bazystef08/Infoeducatie-2026-BazyQ-Automated-Irrigation-System/PPT/2.png

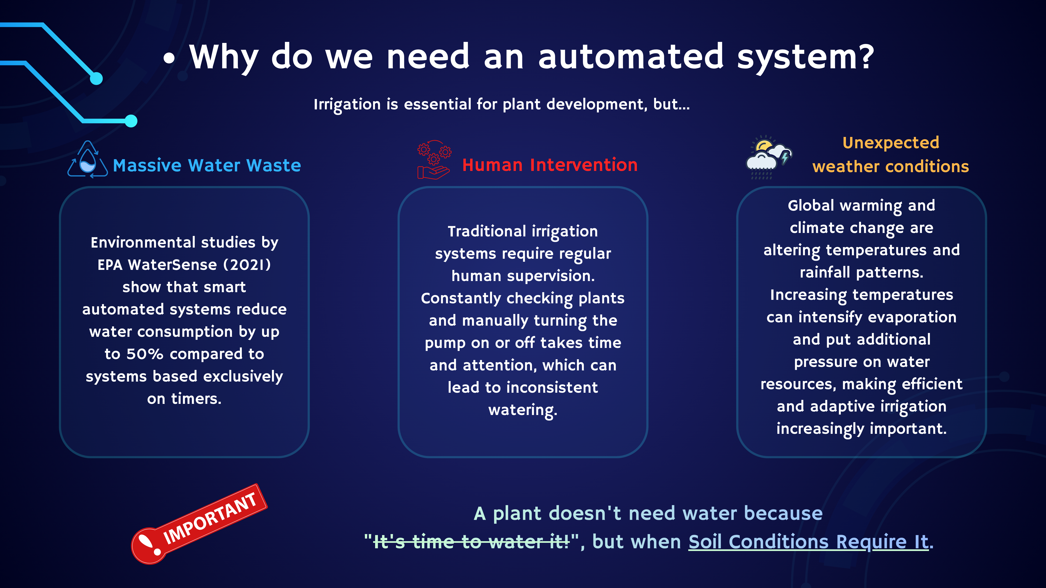
PPT/2.png
