bazystef08/Infoeducatie-2026-BazyQ-Automated-Irrigation-System/PPT/3.png

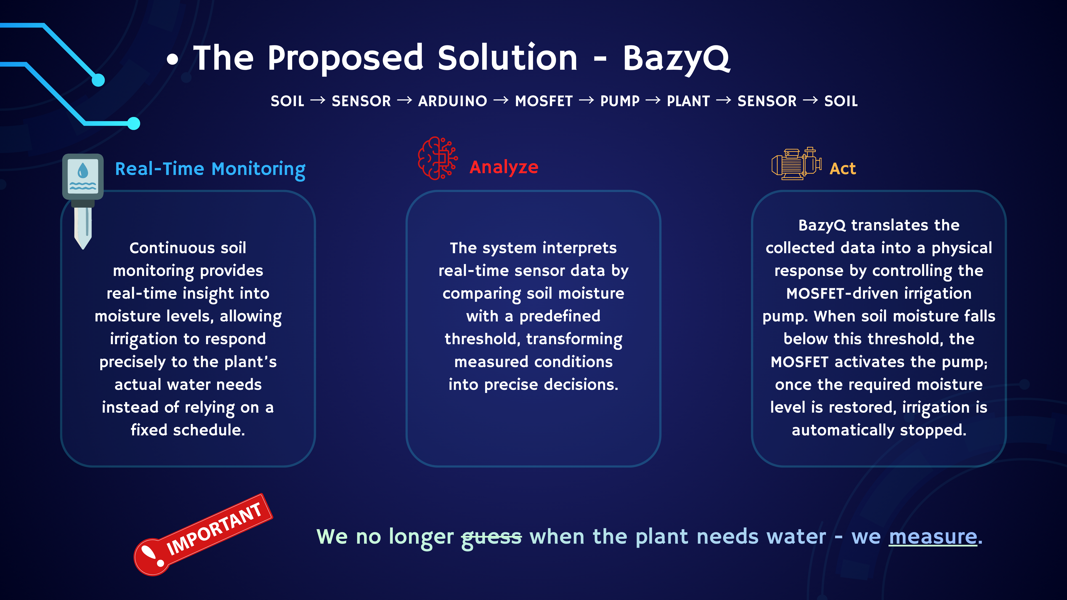
PPT/3.png
