bazystef08/Infoeducatie-2026-BazyQ-Automated-Irrigation-System/PPT/4.png

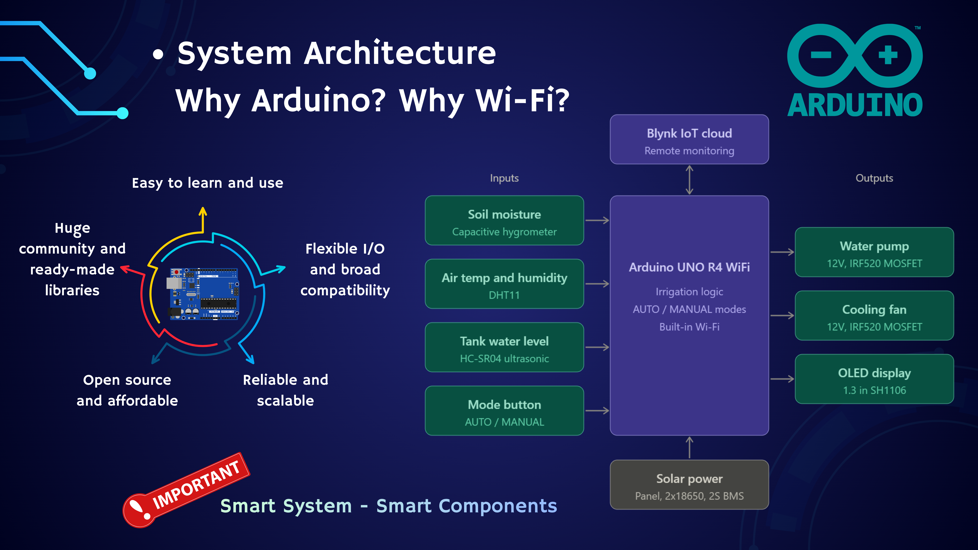
PPT/4.png
