bazystef08/Infoeducatie-2026-BazyQ-Automated-Irrigation-System/Robot Photos/1.jpeg

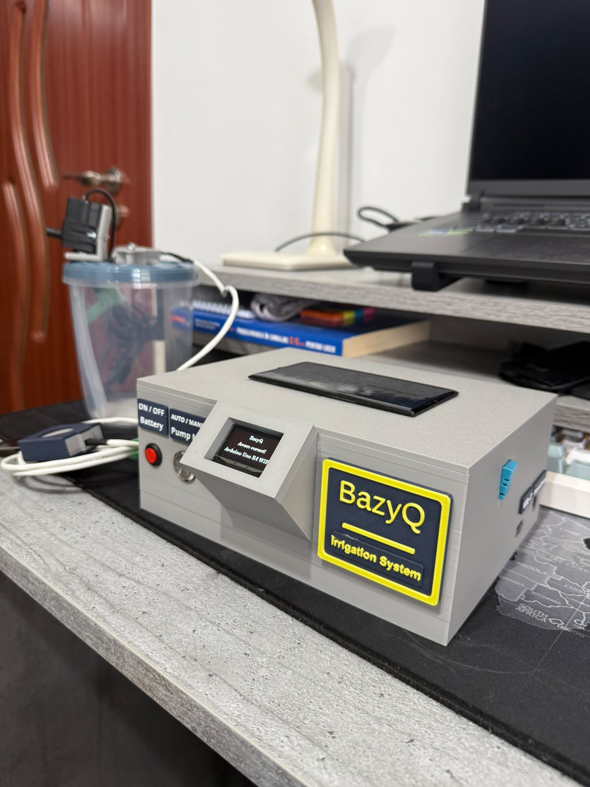
Robot Photos/1.jpeg
