bazystef08/Infoeducatie-2026-BazyQ-Automated-Irrigation-System/Robot Photos/2.jpeg

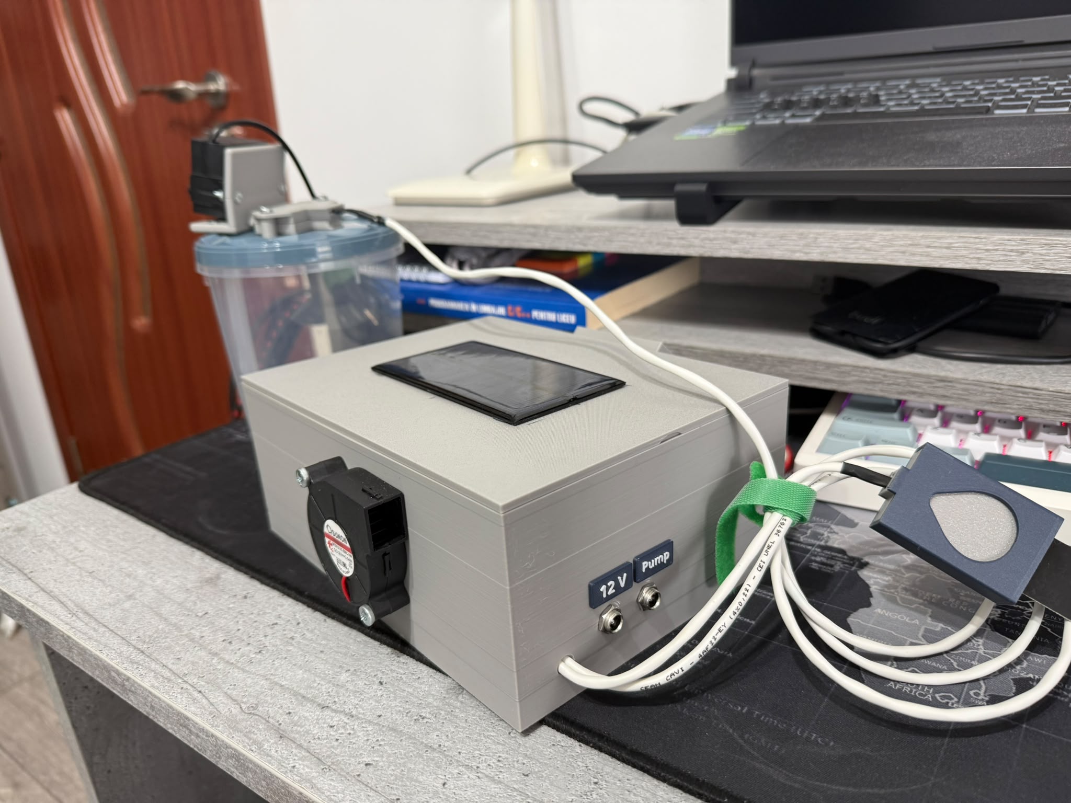
Robot Photos/2.jpeg
