bazystef08/Infoeducatie-2026-BazyQ-Automated-Irrigation-System/Robot Photos/3.jpeg

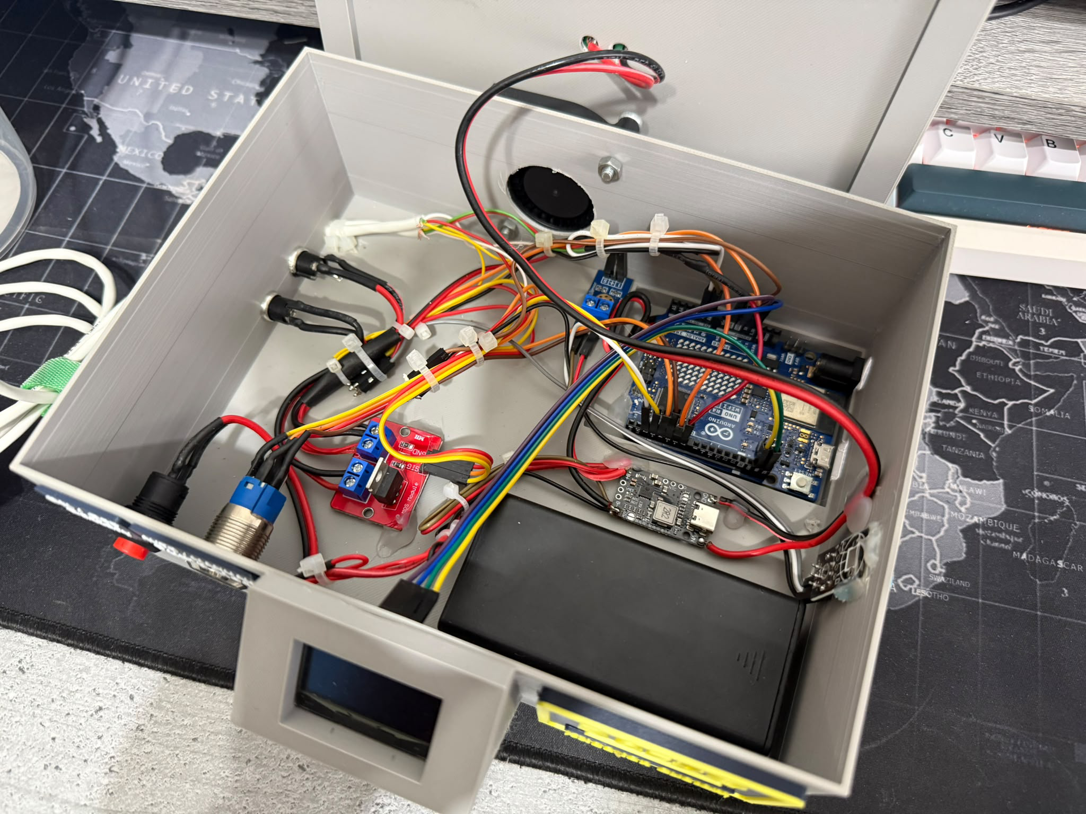
Robot Photos/3.jpeg
