bazystef08/Infoeducatie-2026-BazyQ-Automated-Irrigation-System/Robot Photos/4.png

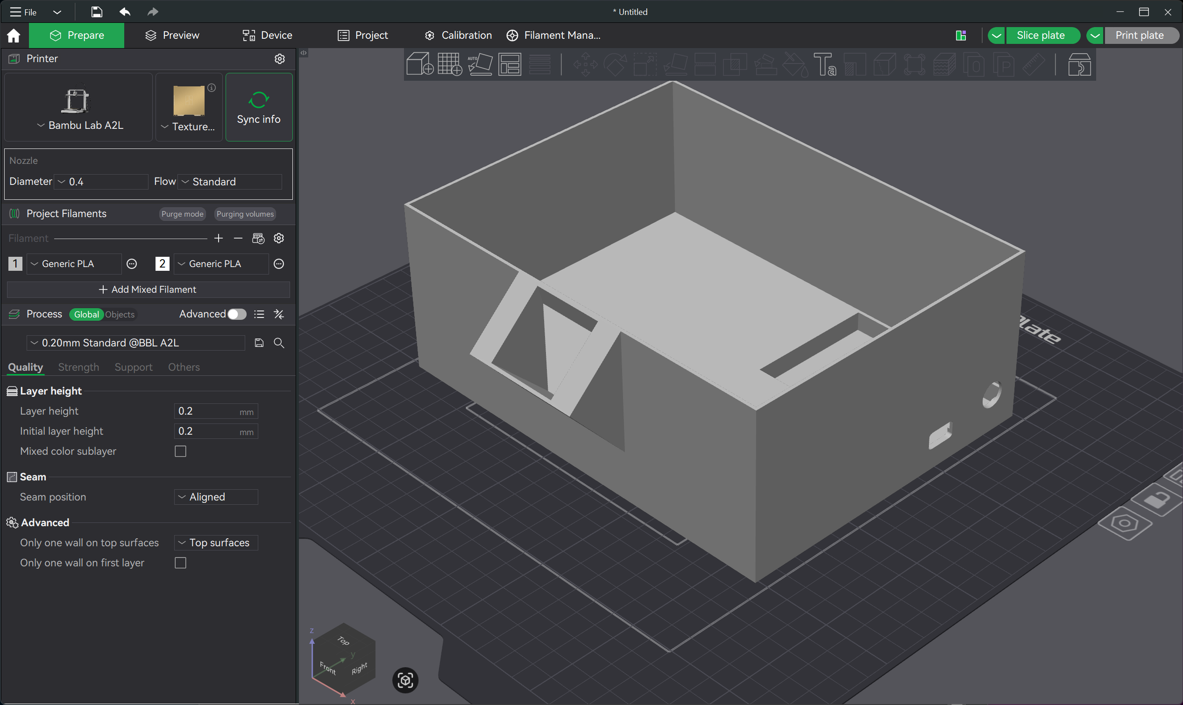
Robot Photos/4.png
