bazystef08/Infoeducatie-2026-BazyQ-Automated-Irrigation-System/Robot Photos/5.png

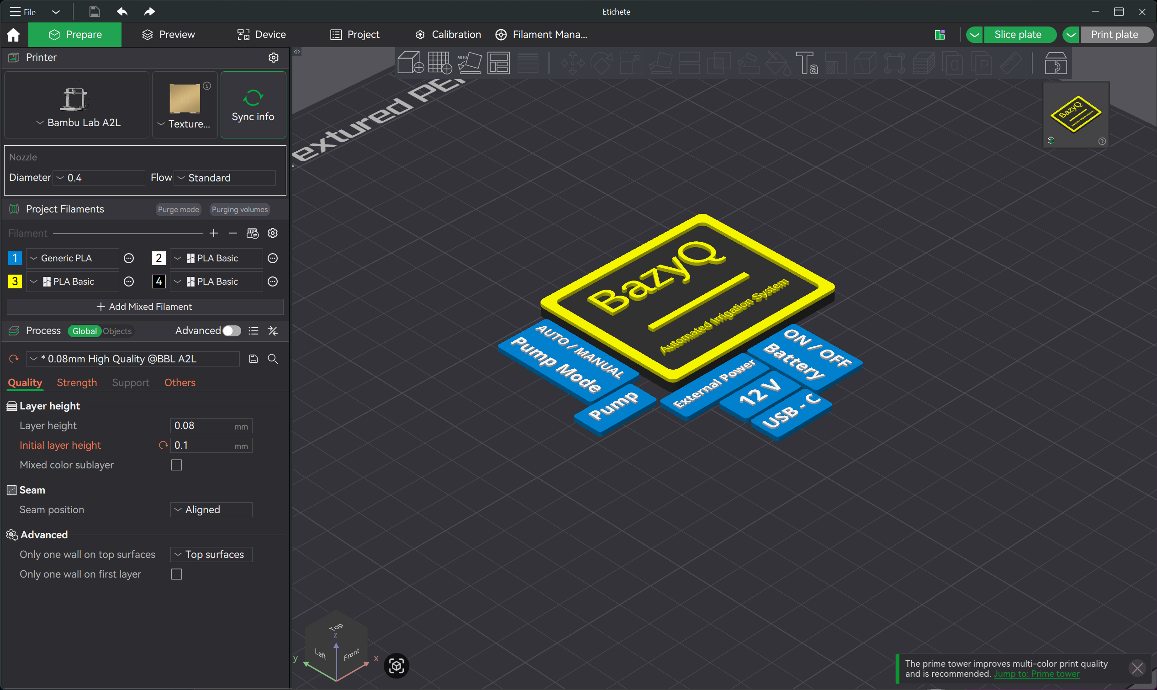
Robot Photos/5.png
