bazystef08/Infoeducatie-2026-BazyQ-Automated-Irrigation-System/Robot Photos/6.png

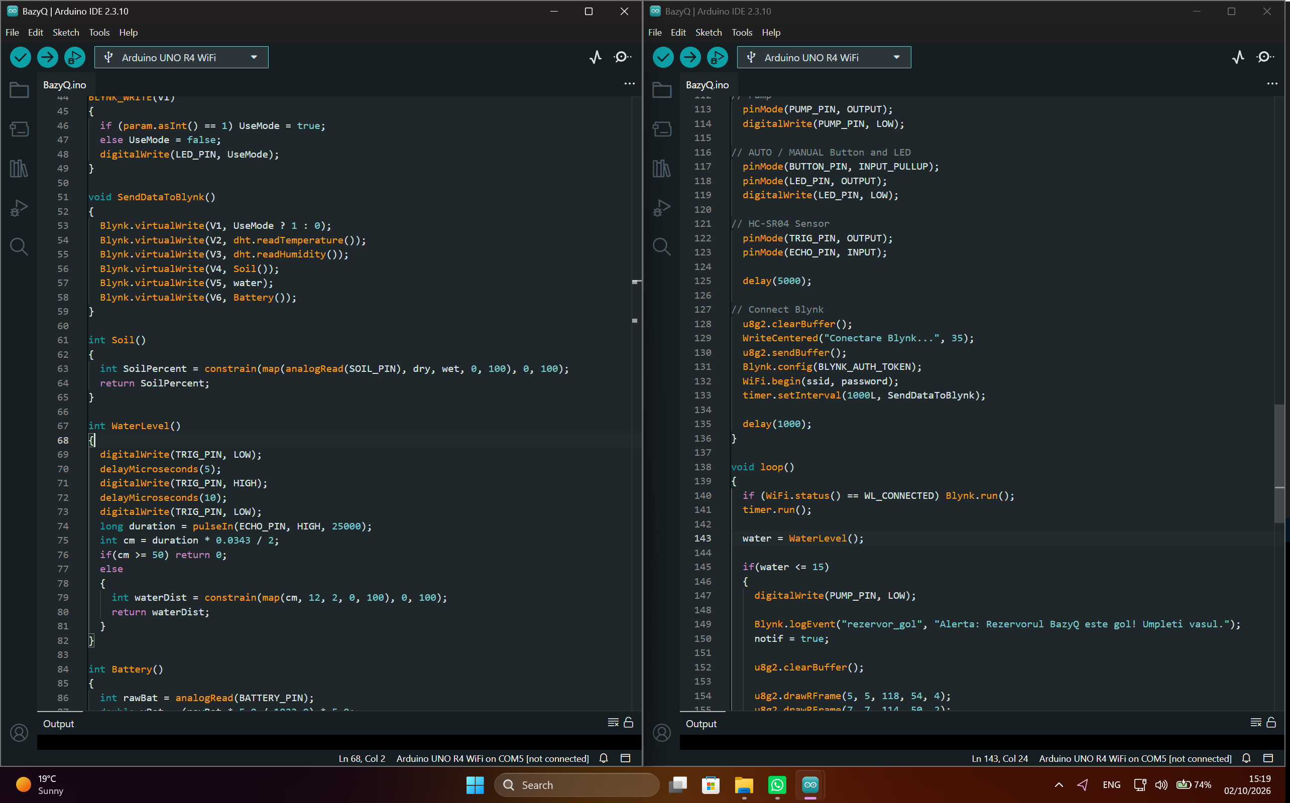
Robot Photos/6.png
